KCayo/Mechanical.Engineering-Senior.Design/CAD Files/Old CAD Files/Ball-Joint 3D Files/Ball.SLDPRT

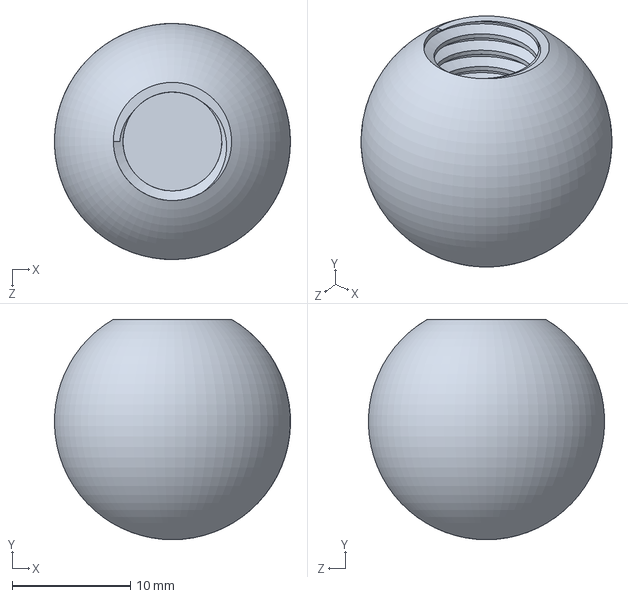
[picture p15: CAD file, 2023-05-16, an earlier design]
CAD Files/Old CAD Files/Ball-Joint 3D Files/Ball.SLDPRT
20.0 x 18.7 x 20.0 mm
