KCayo/Mechanical.Engineering-Senior.Design/CAD Files/Old CAD Files/Linear Spring 3D Files/Linear Spring Bottom Half.SLDPRT

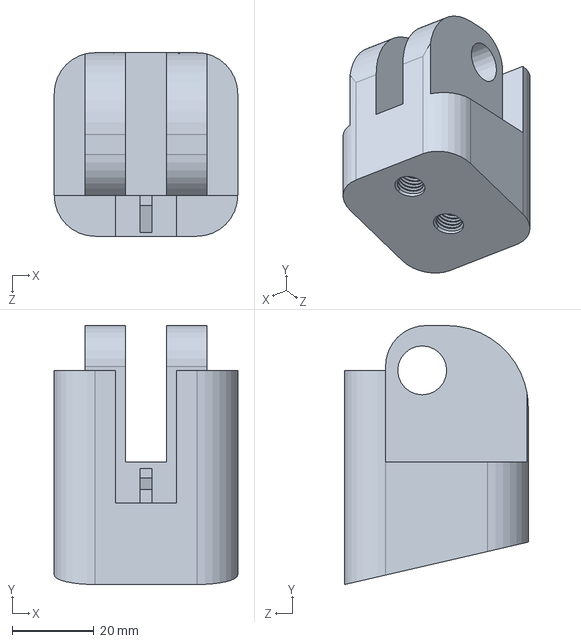
[picture p16: CAD file, 2023-05-16, an earlier design]
CAD Files/Old CAD Files/Linear Spring 3D Files/Linear Spring Bottom Half.SLDPRT
45.0 x 63.5 x 45.0 mm
