KCayo/Mechanical.Engineering-Senior.Design/CAD Files/Old CAD Files/Torsional Spring 3D Files/Torsional Spring Bottom Half.SLDPRT

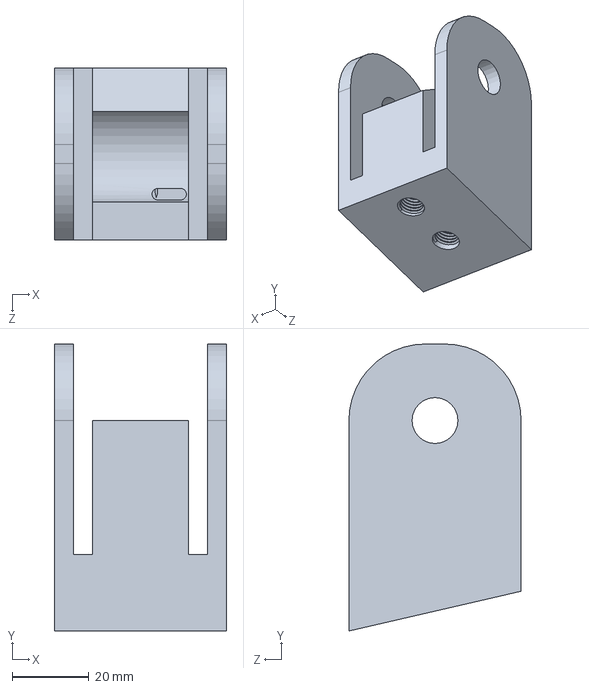
[picture p17: CAD file, 2023-05-16, an earlier design]
CAD Files/Old CAD Files/Torsional Spring 3D Files/Torsional Spring Bottom Half.SLDPRT
45.0 x 75.0 x 45.0 mm
