KCayo/Mechanical.Engineering-Senior.Design/CAD Files/Old CAD Files/Linear Spring 3D Files/Linear Spring Pin.SLDPRT

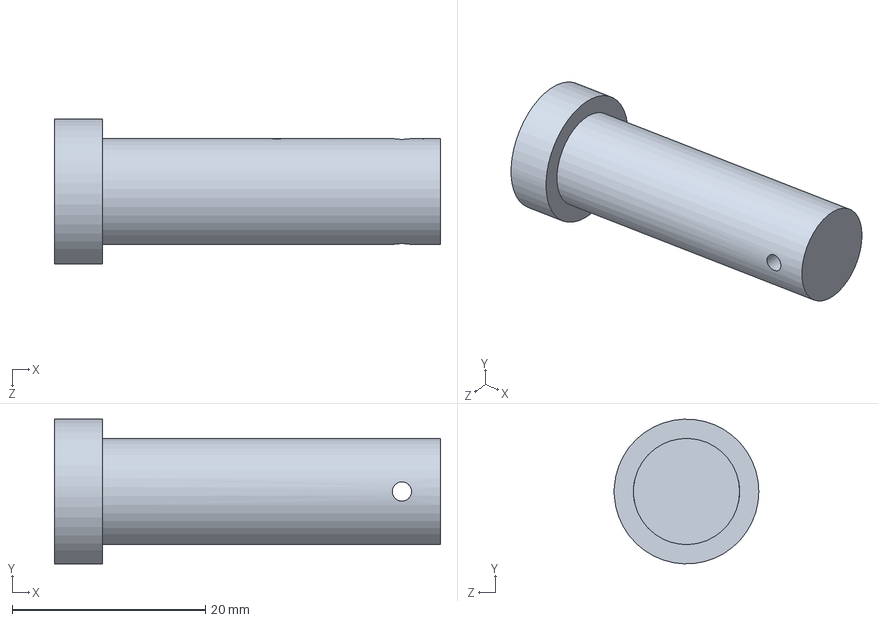
[picture p18: CAD file, 2023-05-16, an earlier design]
CAD Files/Old CAD Files/Linear Spring 3D Files/Linear Spring Pin.SLDPRT
40.0 x 15.0 x 15.0 mm
